cepdnaclk/e17-3yp-remote-keyboard-tutoring-system/Research/Backend Technologies/Nginx/README.md

# Why Choose NGINX?
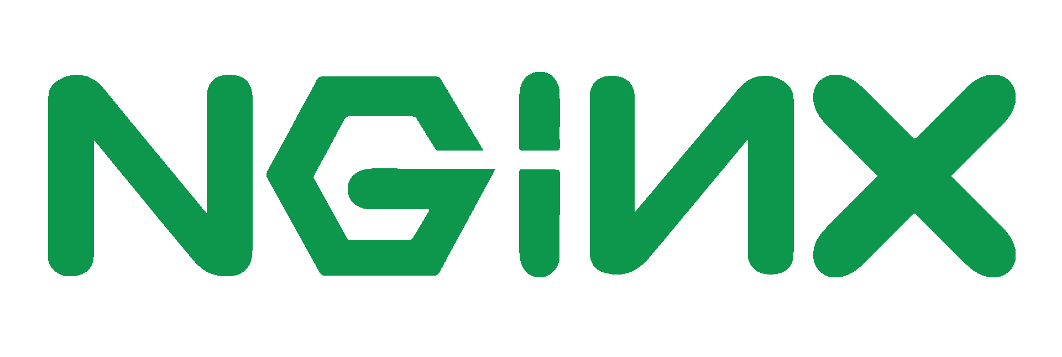
[picture p58: Research/Backend Technologies/Nginx/images/nginx_logo.png]


## What is NGINX ?
NGINX is open source software for web serving, reverse proxying, caching, load balancing, media streaming, and more. It started out as a web server designed for maximum performance and stability. In addition to its HTTP server capabilities, NGINX can also function as a proxy server for email (IMAP, POP3, and SMTP) and a reverse proxy and load balancer for HTTP, TCP, and UDP servers.

## Features of NGINX

- As a software‑only all-in-one load balancer, web server, API gateway, and reverse proxy that is designed for cloud‑native architectures, NGINX helps you accelerate your IT infrastructure and application modernization efforts. NGINX Plus delivers enterprise‑grade capabilities that provide robust reliability and security.
- NGINX is a multifunction tool. With NGINX, you can use the same tool as your load balancer, reverse proxy, content cache, and web server, minimizing the amount of tooling and configuration your organization needs to maintain. NGINX offers documentation and a wide array of eBooks, webinars, and videos to get you on your feet. NGINX Plus includes rapid‑response customer support, so you can easily get help diagnosing any part of your stack that uses NGINX or NGINX Plus.
- NGINX keeps evolving. For the past decade NGINX has been at the forefront of development of the modern Web, and has helped lead the way on everything from HTTP/2 to microservices support. As development and delivery of web applications continue to evolve, NGINX Plus keeps adding features to enable flawless application delivery, from support for configuration using an implementation of JavaScript customized for NGINX, to support for dynamic modules. Using NGINX Plus ensures you’ll stay at the cutting edge of web performance.

## How NGINX benefit Us ?
We will be using NGINX as a reverse proxy so that we can access it through http, https along with Let’s Encrypt to create and manage free validated SSL/TLS certificates. 

It’s well known that SSL/TLS encryption of your website leads to higher search rankings and better security for your users. However, there are a number of barriers that have prevented website owners from adopting SSL.Two of the biggest barriers have been the cost and the manual processes involved in getting a certificate. But now, with Let’s Encrypt, they are no longer a concern. Let’s Encrypt makes SSL/TLS encryption freely available to everyone.

### Let's Encrypt -
is a free, automated, and open certificate authority (CA). Certificates issued by Let’s Encrypt are trusted by most browsers today, including older browsers such as Internet Explorer on Windows XP SP3. In addition, Let’s Encrypt fully automates both issuing and renewing of certificates.

**[click here](#) to see how we deply our apps, APIs with NGINX and Let's Encrypt**
