cepdnaclk/e17-3yp-remote-keyboard-tutoring-system/docs/images/about02.gif

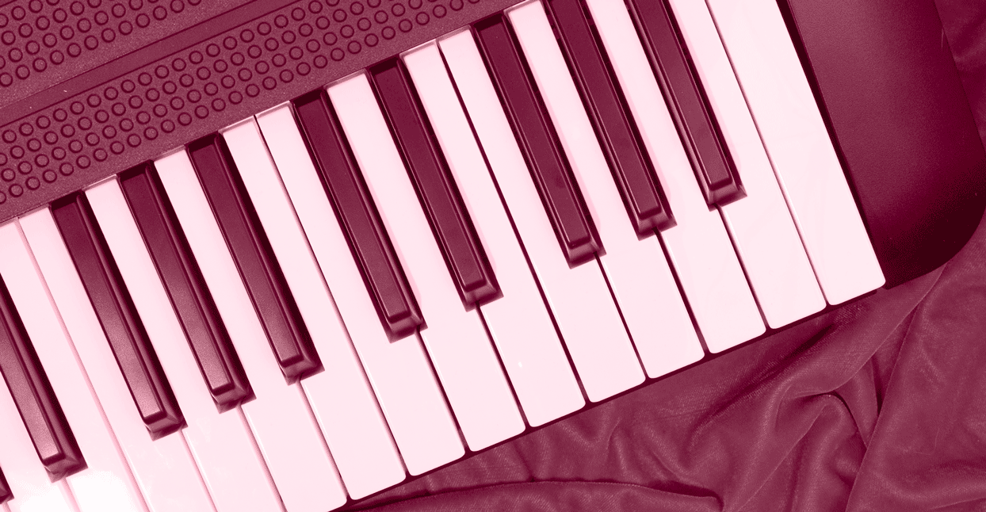
docs/images/about02.gif
