cepdnaclk/e17-3yp-remote-keyboard-tutoring-system/docs/images/about-2.jpg

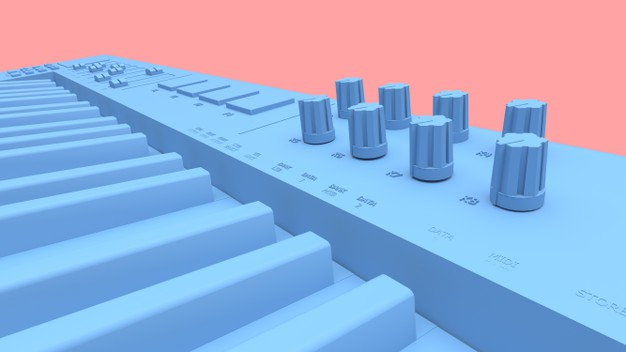
docs/images/about-2.jpg
