cepdnaclk/e17-3yp-remote-keyboard-tutoring-system/docs/images/FlowOfData1.png

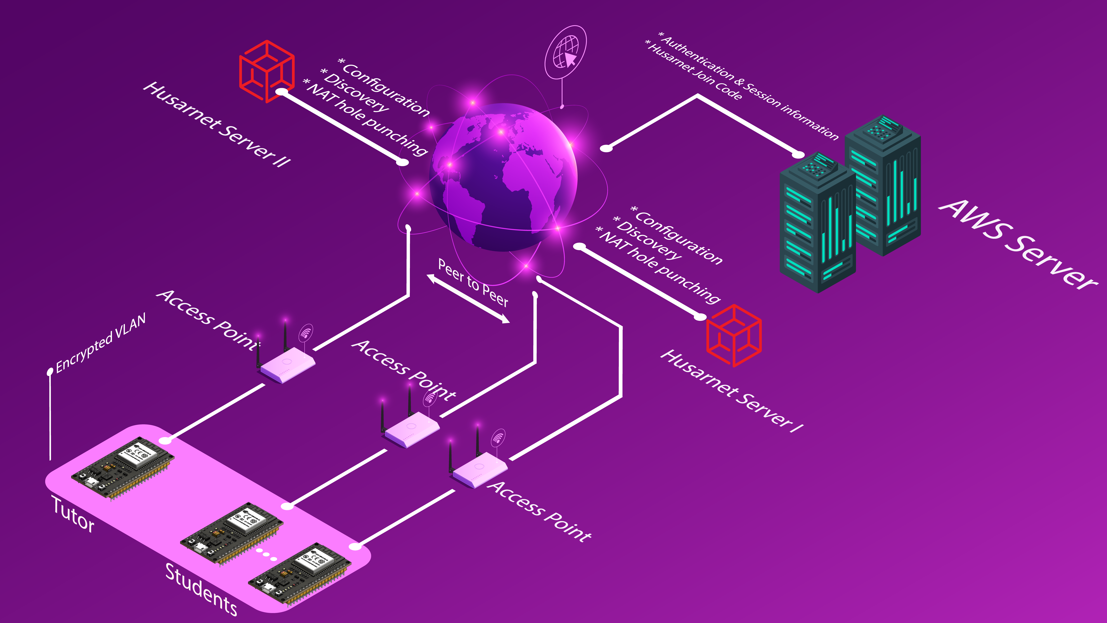
docs/images/FlowOfData1.png
