cepdnaclk/e17-3yp-remote-keyboard-tutoring-system/docs/images/MobileUIgif.gif

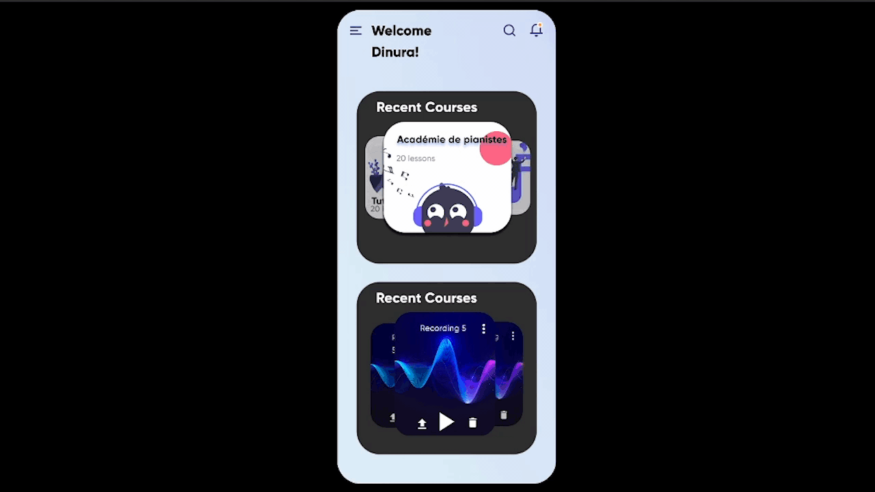
docs/images/MobileUIgif.gif
