cepdnaclk/e17-3yp-remote-keyboard-tutoring-system/docs/images/placeholder-mobile.png

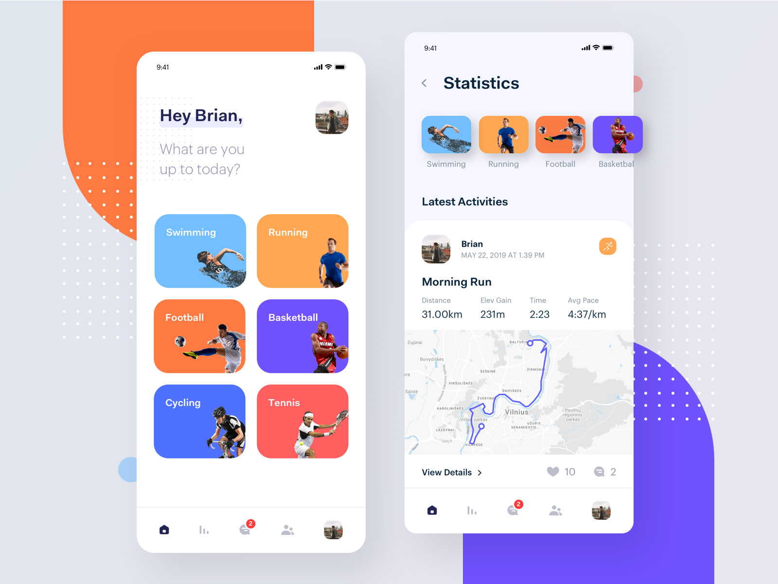
docs/images/placeholder-mobile.png
