cepdnaclk/e17-3yp-remote-keyboard-tutoring-system/docs/images/placeholder-web.png

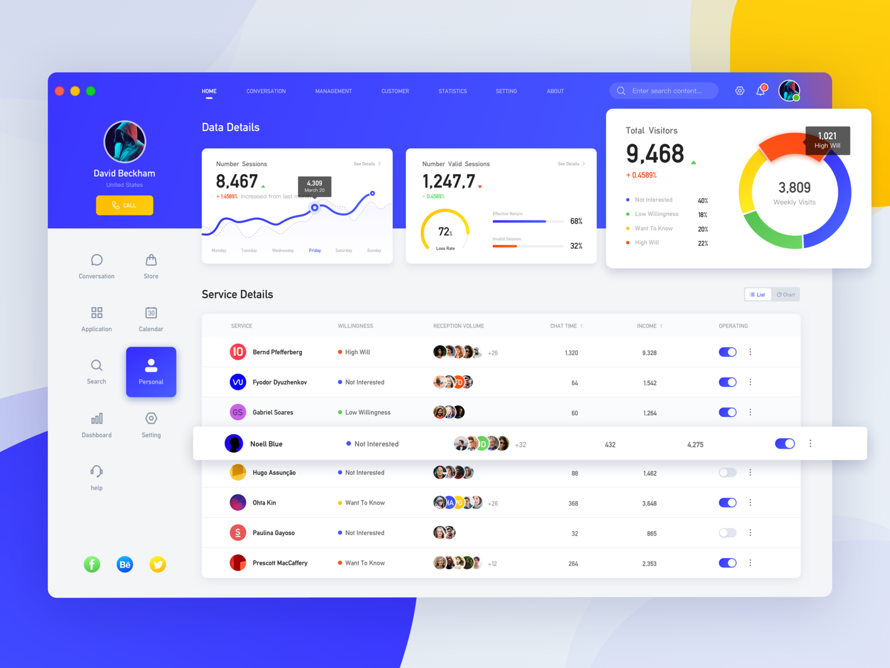
docs/images/placeholder-web.png
