cepdnaclk/e17-3yp-remote-keyboard-tutoring-system/docs/images/Processing Unit 2.jpg

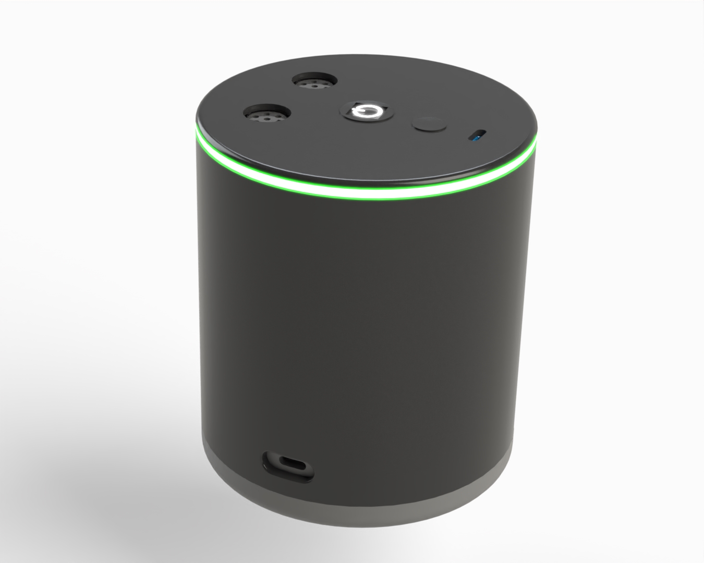
docs/images/Processing Unit 2.jpg
