cepdnaclk/e17-3yp-remote-keyboard-tutoring-system/docs/images/pu.png

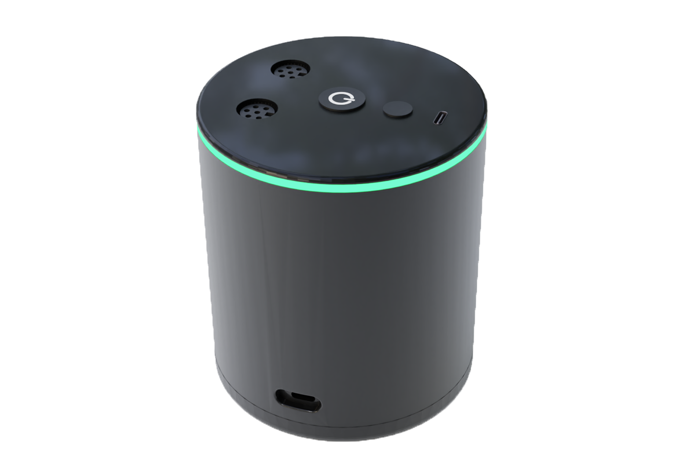
docs/images/pu.png
