cepdnaclk/e17-3yp-remote-keyboard-tutoring-system/docs/images/Remote-Keyboard-Tutor.gif

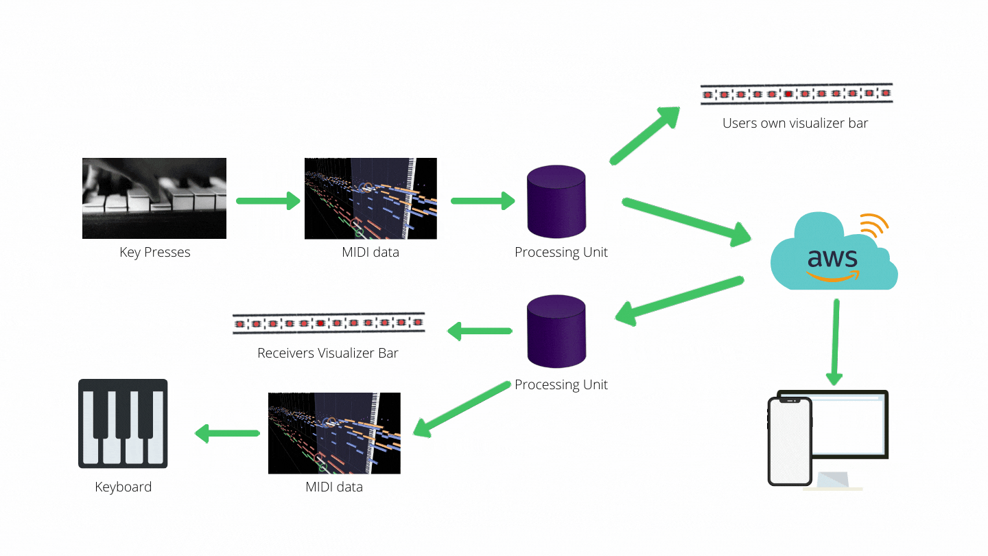
docs/images/Remote-Keyboard-Tutor.gif
