cepdnaclk/e17-3yp-remote-keyboard-tutoring-system/docs/images/Remote-Keyboard-Tutor.png

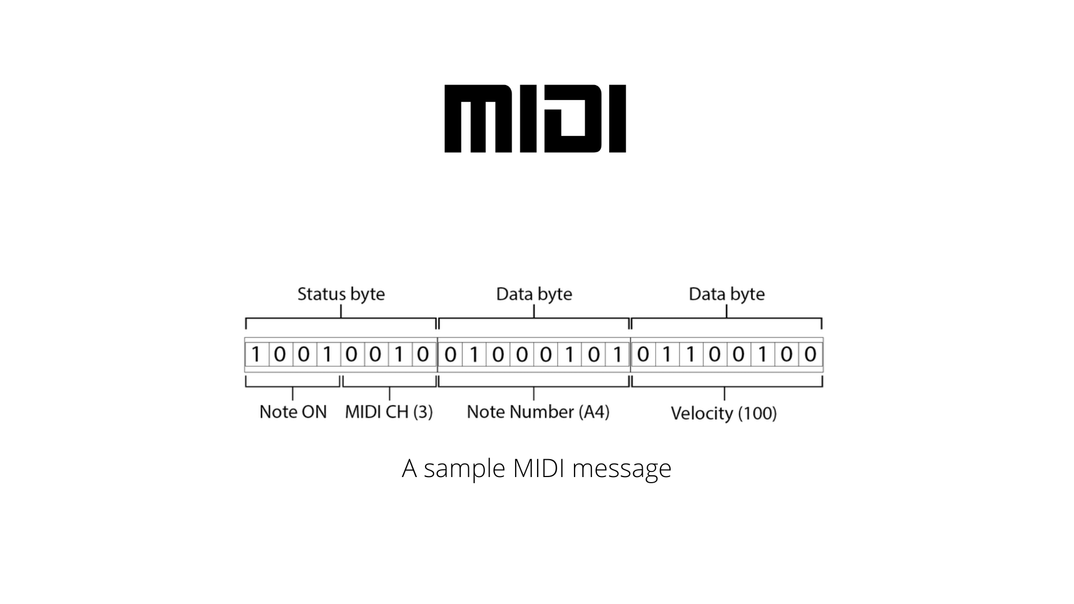
docs/images/Remote-Keyboard-Tutor.png
