cepdnaclk/e17-3yp-remote-keyboard-tutoring-system/docs/images/view1.png

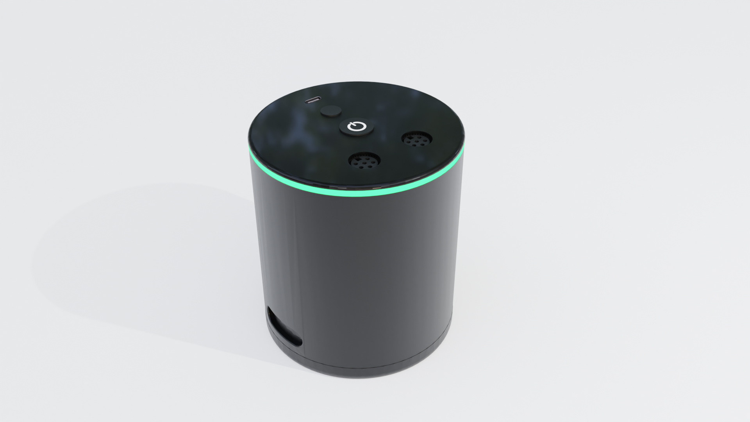
docs/images/view1.png
