cepdnaclk/e17-3yp-remote-keyboard-tutoring-system/docs/images/view3.png

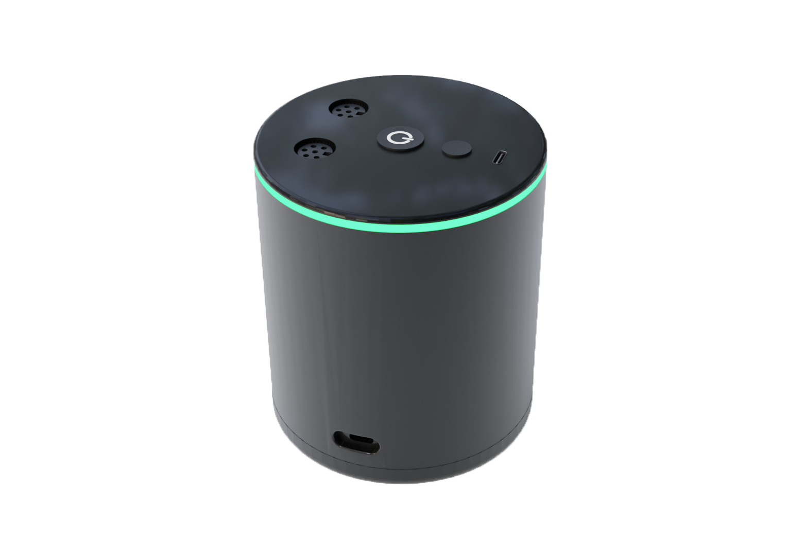
docs/images/view3.png
