cepdnaclk/e17-3yp-remote-keyboard-tutoring-system/docs/images/Visualizer Block.jpg

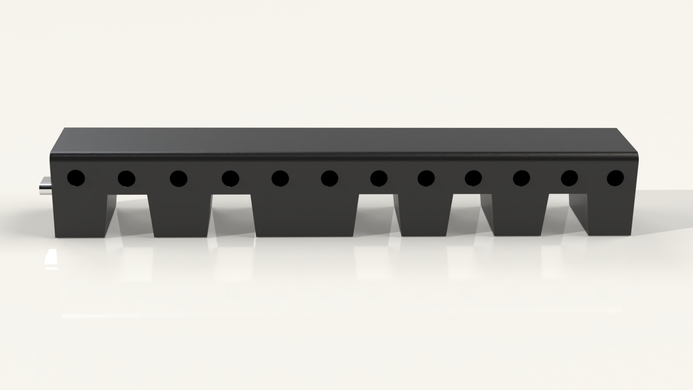
docs/images/Visualizer Block.jpg
