cepdnaclk/e17-3yp-remote-keyboard-tutoring-system/docs/images/visualizerBaeW.png

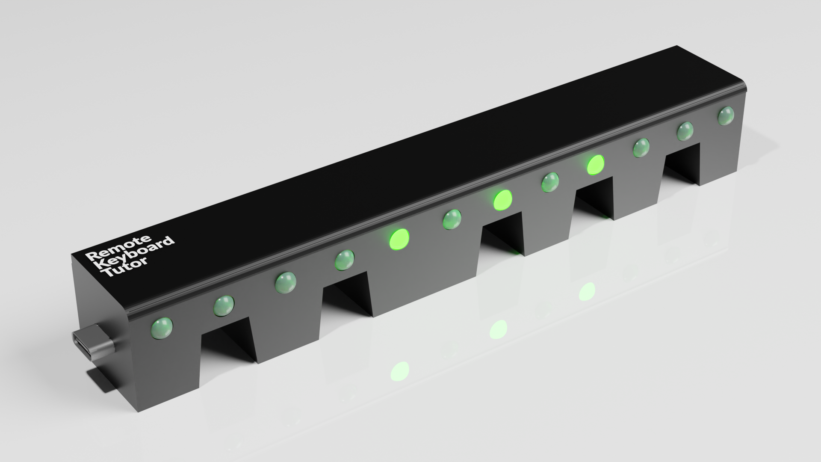
docs/images/visualizerBaeW.png
