cepdnaclk/e17-3yp-remote-keyboard-tutoring-system/docs/images/visualizerBar.png

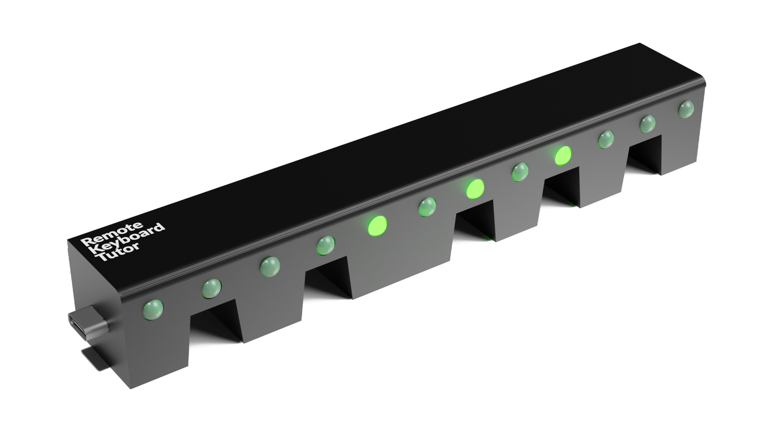
docs/images/visualizerBar.png
