cepdnaclk/e17-3yp-remote-keyboard-tutoring-system/docs/images/visualizerBarB.png

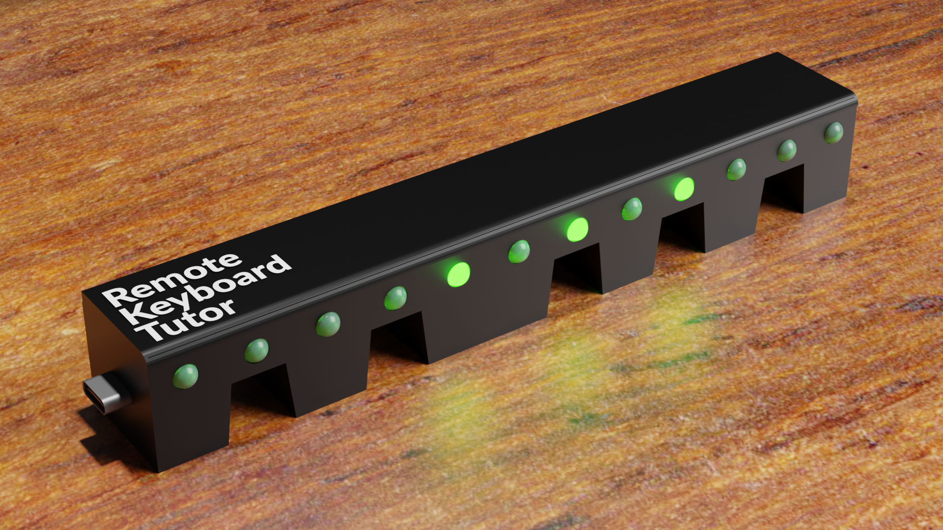
docs/images/visualizerBarB.png
