cepdnaclk/e17-3yp-remote-keyboard-tutoring-system/docs/midi-message-taxonomy.png

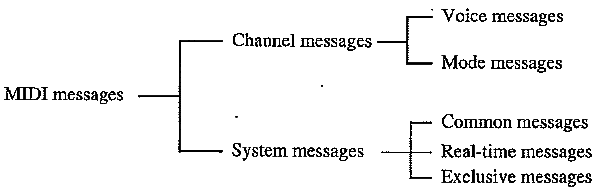
docs/midi-message-taxonomy.png
