cepdnaclk/e17-3yp-remote-keyboard-tutoring-system/docs/protocol.png

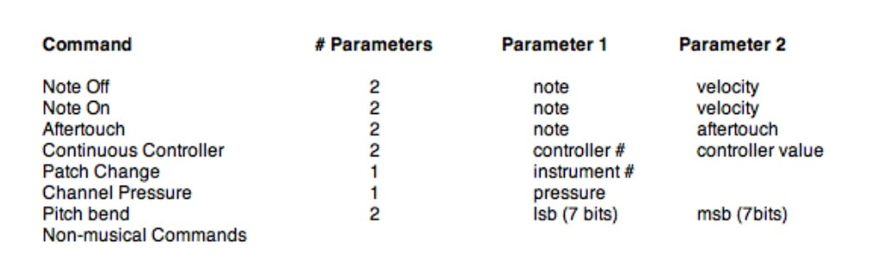
docs/protocol.png
