cepdnaclk/e17-3yp-remote-keyboard-tutoring-system/Hardware/Schematics/Arduino-Pro-Micro-Pinout.jpg

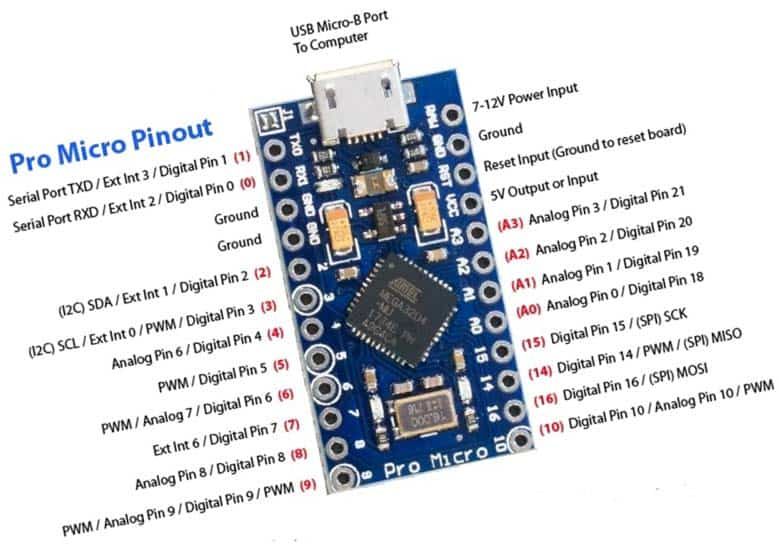
Hardware/Schematics/Arduino-Pro-Micro-Pinout.jpg
