cepdnaclk/e17-3yp-remote-keyboard-tutoring-system/Hardware/Schematics/DIN 5 pin connector pinout.jpg

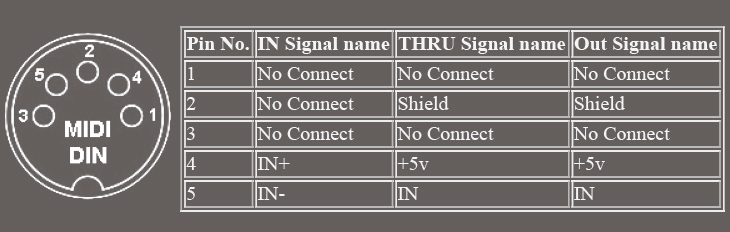
Hardware/Schematics/DIN 5 pin connector pinout.jpg
