cepdnaclk/e17-3yp-remote-keyboard-tutoring-system/Hardware/Schematics/pro-mini-pinout.jpeg

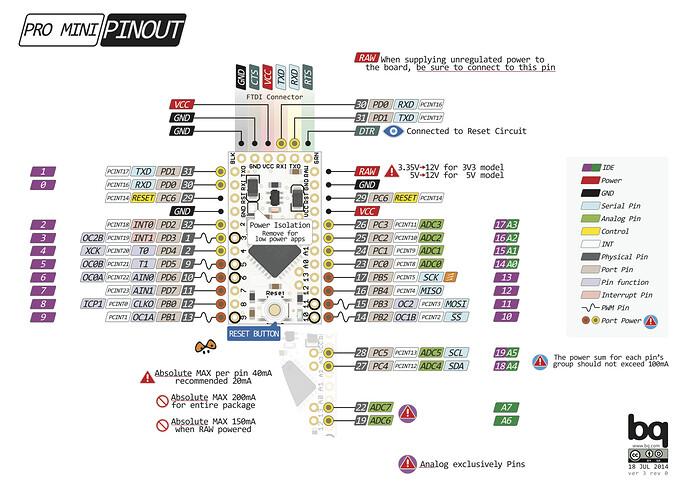
Hardware/Schematics/pro-mini-pinout.jpeg
