cepdnaclk/e17-3yp-remote-keyboard-tutoring-system/Hardware/Schematics/Processing Unit.png

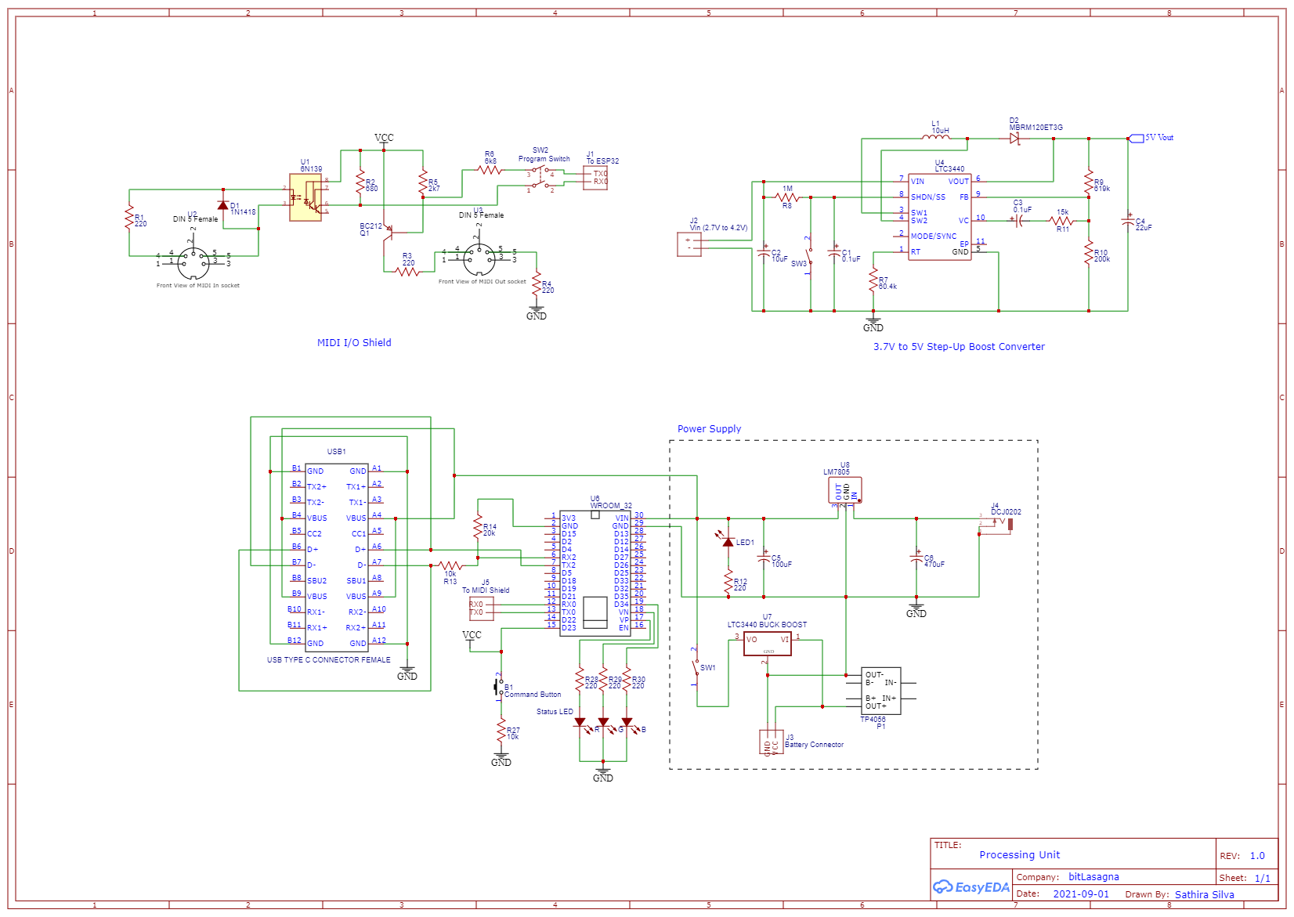
Hardware/Schematics/Processing Unit.png
