cepdnaclk/e17-3yp-remote-keyboard-tutoring-system/Mobile App/ForteApp/MobileApp/assets/3e8c7e1767d023deecac1b5b417257c0.jpg

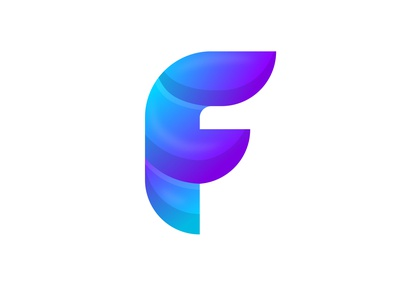
Mobile App/ForteApp/MobileApp/assets/3e8c7e1767d023deecac1b5b417257c0.jpg
