cepdnaclk/e17-3yp-remote-keyboard-tutoring-system/Mobile App/ForteApp/MobileApp/assets/home.png

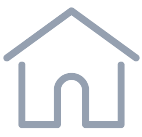
Mobile App/ForteApp/MobileApp/assets/home.png
