cepdnaclk/e17-3yp-remote-keyboard-tutoring-system/Mobile App/ForteApp/MobileApp/assets/M2.jpg

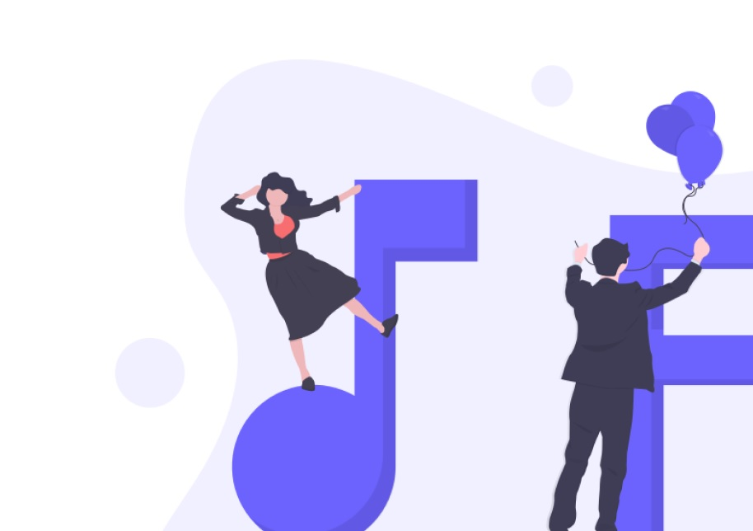
Mobile App/ForteApp/MobileApp/assets/M2.jpg
