cepdnaclk/e17-3yp-remote-keyboard-tutoring-system/Mobile App/ForteApp/MobileApp/assets/M3.jpg

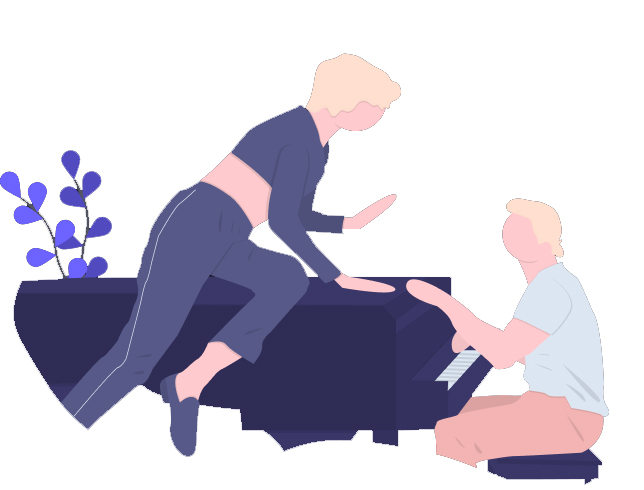
Mobile App/ForteApp/MobileApp/assets/M3.jpg
