cepdnaclk/e17-3yp-remote-keyboard-tutoring-system/Mobile App/ForteApp/MobileApp/assets/settings.png

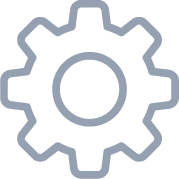
Mobile App/ForteApp/MobileApp/assets/settings.png
