cepdnaclk/e17-3yp-remote-keyboard-tutoring-system/server/src/database_schema/forte-er.jpeg

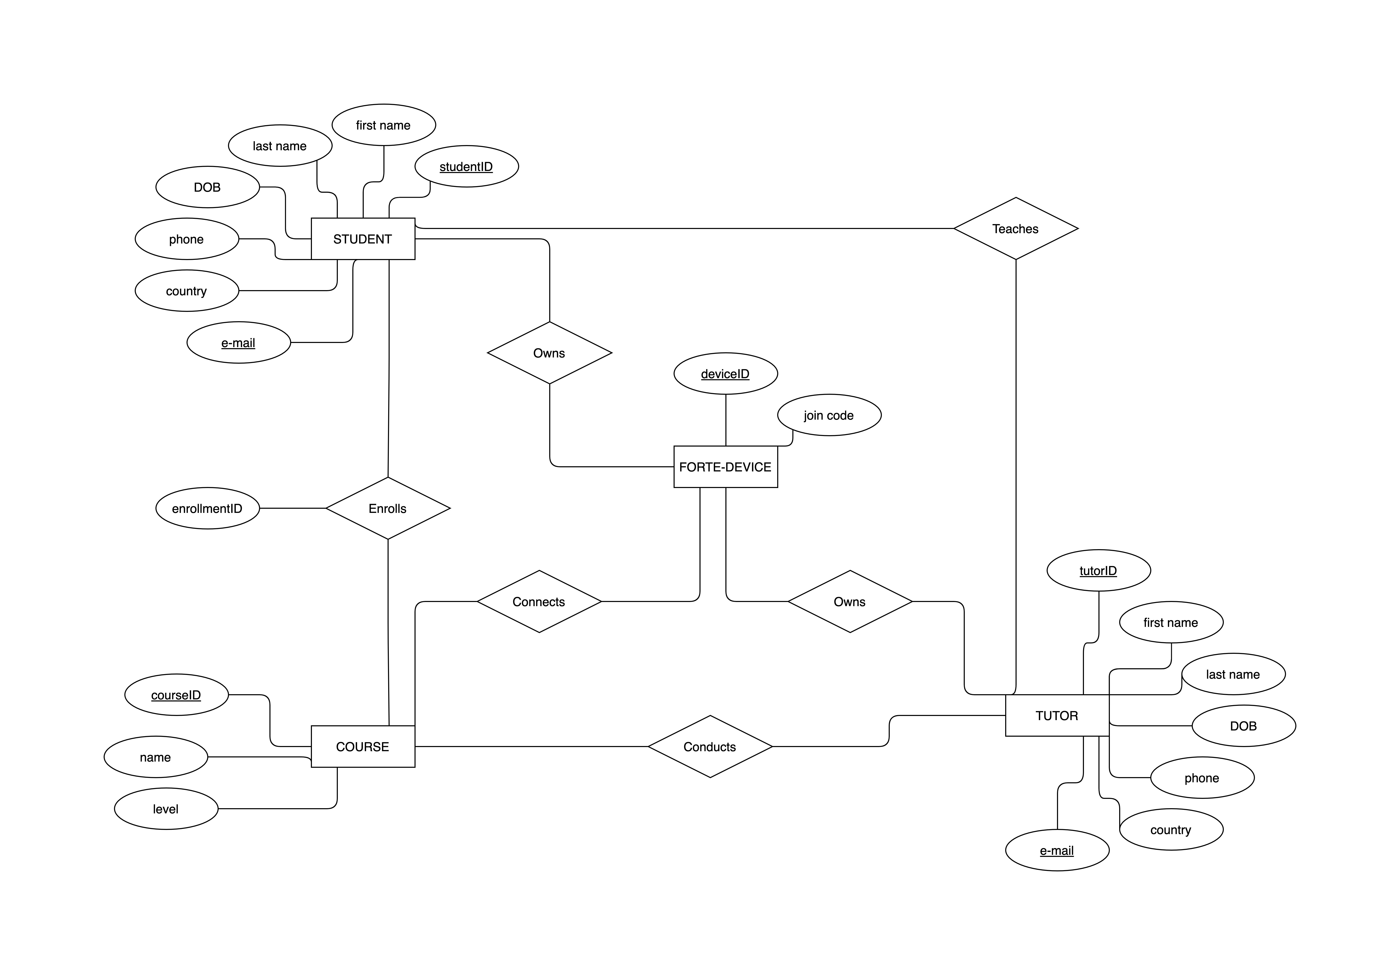
server/src/database_schema/forte-er.jpeg
