cepdnaclk/e17-3yp-remote-keyboard-tutoring-system/server/src/uploads/courses/cover-upload_dateVal_1634644308922_photo-1552422535-c45813c61732.jpg

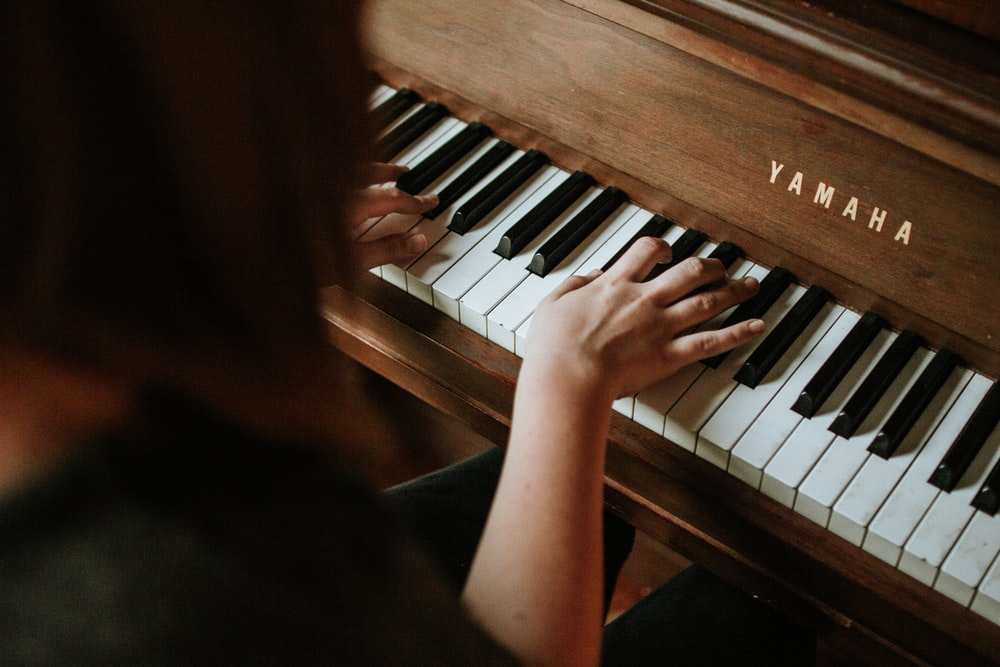
server/src/uploads/courses/cover-upload_dateVal_1634644308922_photo-1552422535-c45813c61732.jpg
