cepdnaclk/e17-3yp-remote-keyboard-tutoring-system/server/src/uploads/courses/cover-upload_dateVal_1634646680036_Piano-Hands-Play-HD-Wallpapers-Free-Download.jpg

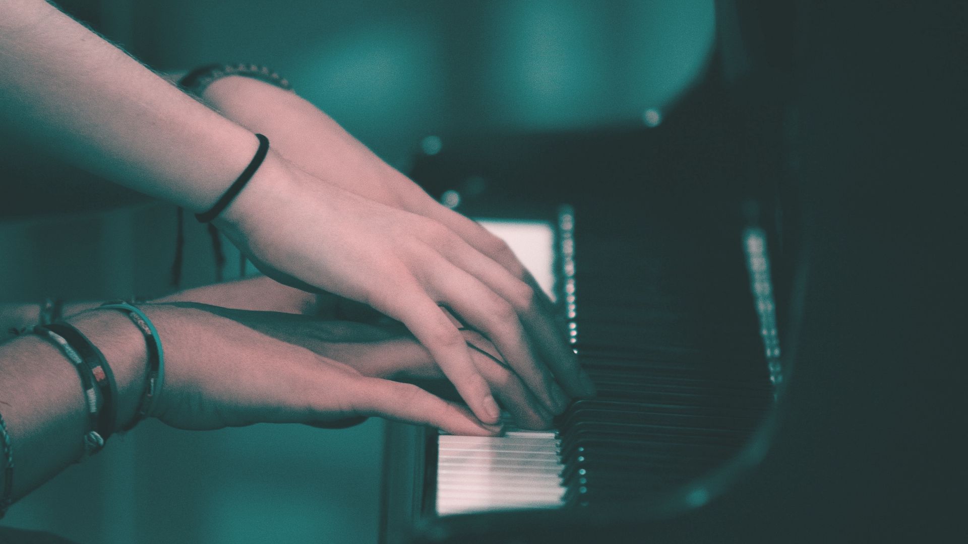
server/src/uploads/courses/cover-upload_dateVal_1634646680036_Piano-Hands-Play-HD-Wallpapers-Free-Download.jpg
