cepdnaclk/e17-3yp-remote-keyboard-tutoring-system/server/src/uploads/courses/cover-upload_dateVal_1634693529020_cd62944dfa67ef2cf75b0063e259fd68.jpg

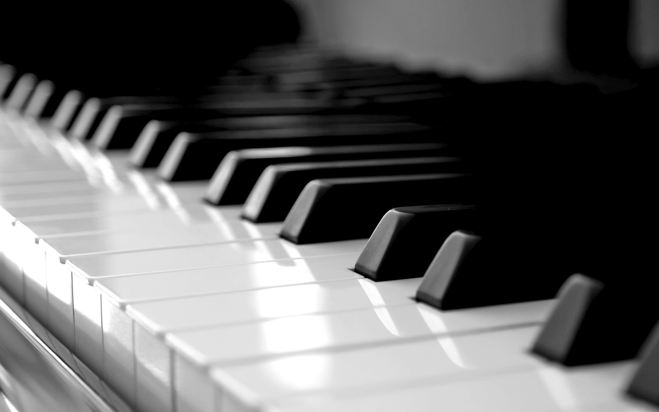
server/src/uploads/courses/cover-upload_dateVal_1634693529020_cd62944dfa67ef2cf75b0063e259fd68.jpg
