cepdnaclk/e17-3yp-remote-keyboard-tutoring-system/server/src/uploads/courses/cover-upload_dateVal_1634815107962_piano-anime.gif

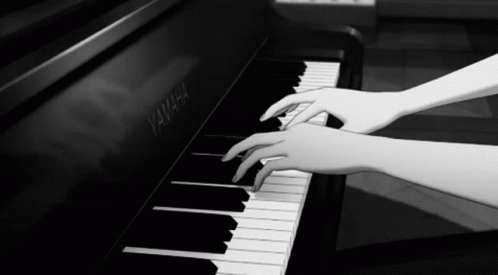
server/src/uploads/courses/cover-upload_dateVal_1634815107962_piano-anime.gif
