cepdnaclk/e17-3yp-remote-keyboard-tutoring-system/server/src/uploads/courses/cover-upload_dateVal_1634815645119_piano-white-classical-lacquer.jpg

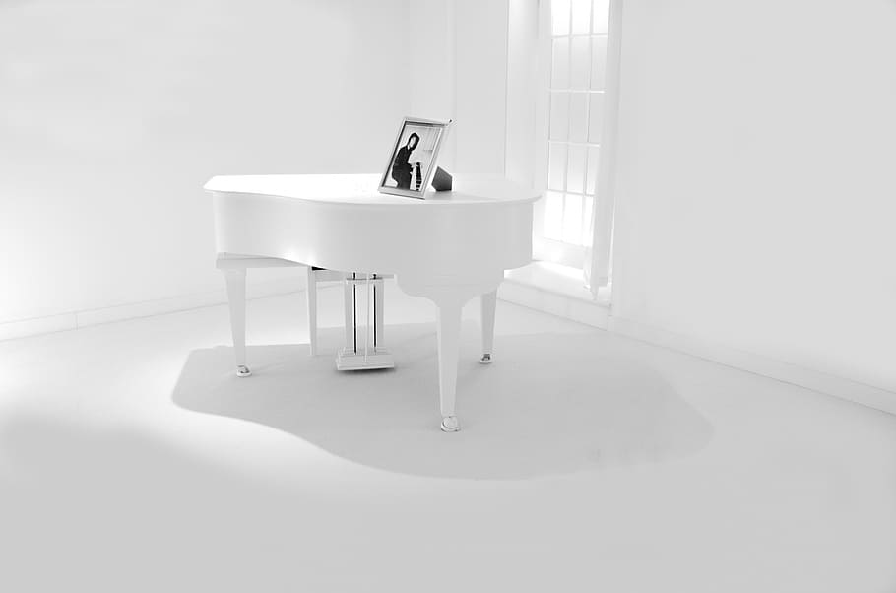
server/src/uploads/courses/cover-upload_dateVal_1634815645119_piano-white-classical-lacquer.jpg
