cepdnaclk/e17-3yp-remote-keyboard-tutoring-system/server/src/uploads/courses/cover-upload_dateVal_1634832013604_Blue-hair-anime-girl-play-piano_2560x1440.jpg

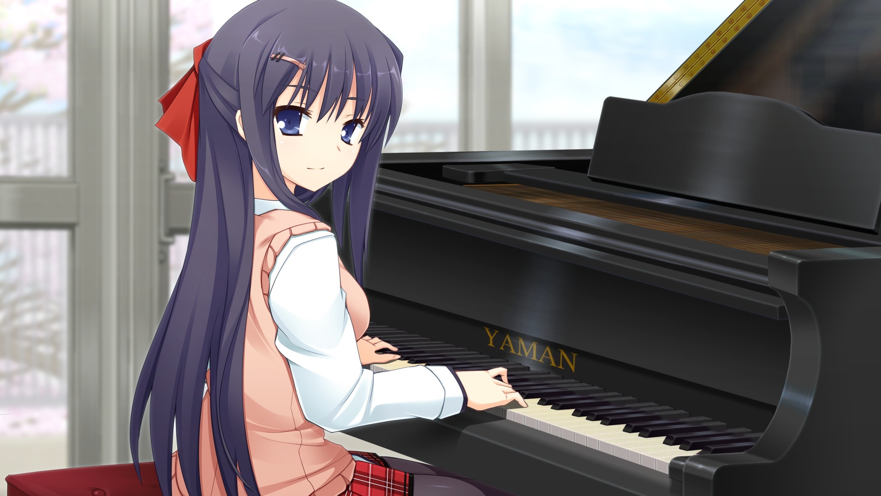
server/src/uploads/courses/cover-upload_dateVal_1634832013604_Blue-hair-anime-girl-play-piano_2560x1440.jpg
