cepdnaclk/e17-3yp-remote-keyboard-tutoring-system/UI-UX/Web/images/First.jpg

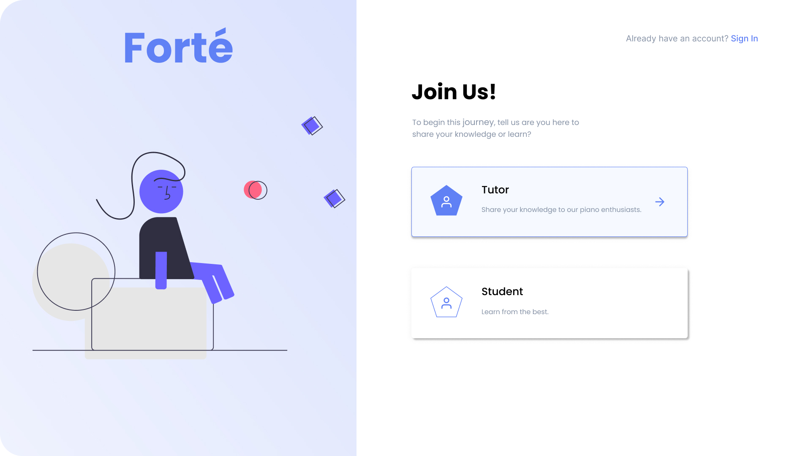
UI-UX/Web/images/First.jpg
