cepdnaclk/e17-3yp-remote-keyboard-tutoring-system/web-app/src/assets/images/Cover 1.jpg

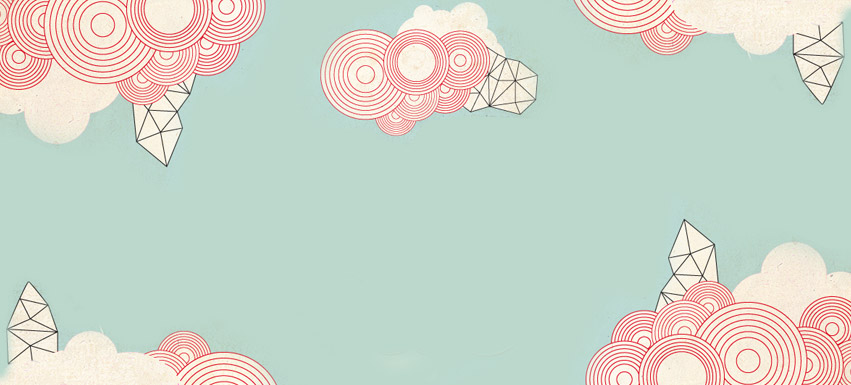
web-app/src/assets/images/Cover 1.jpg
