cepdnaclk/e17-3yp-remote-keyboard-tutoring-system/web-app/src/components/TileList/Default Backgrounds/bg1.jpg

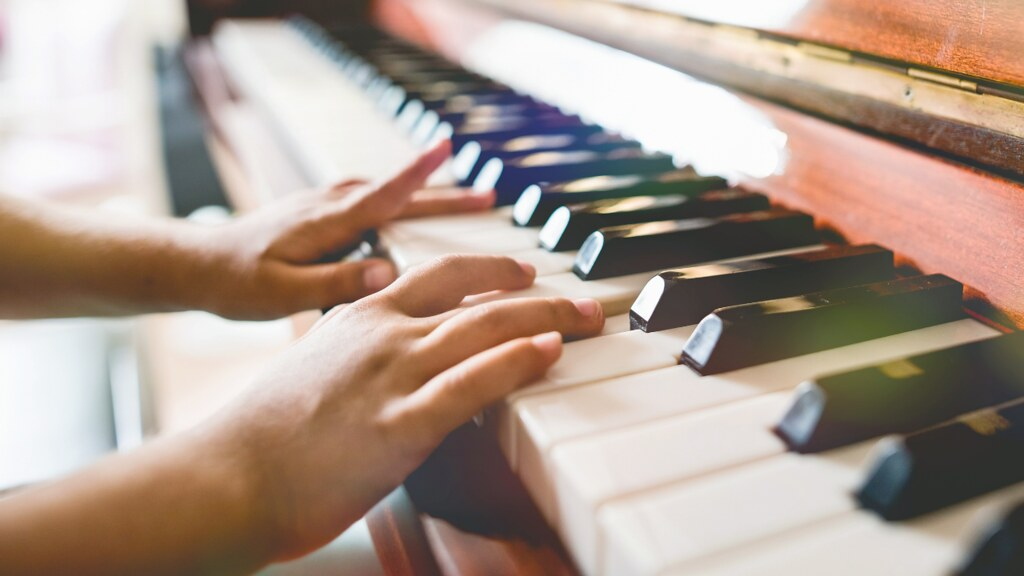
web-app/src/components/TileList/Default Backgrounds/bg1.jpg
