cepdnaclk/e17-3yp-remote-keyboard-tutoring-system/web-app/src/assets/images/email-id-verification.png

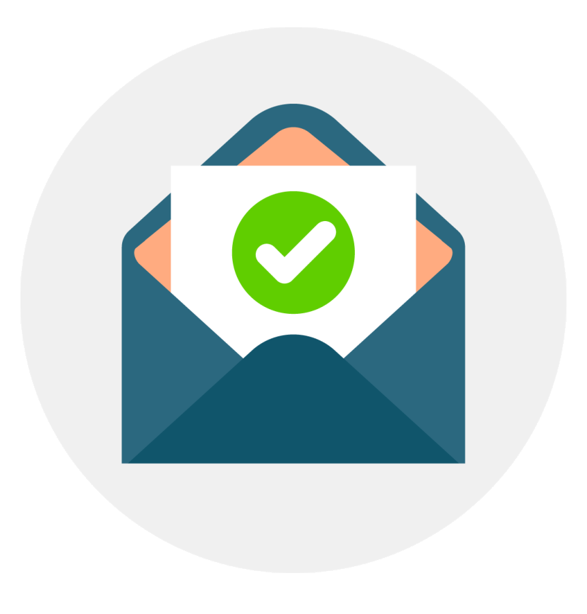
web-app/src/assets/images/email-id-verification.png
