cepdnaclk/e17-3yp-remote-keyboard-tutoring-system/Research/ESP32/ESP-IDF-Tests/wifiConnect/main/main.c

#include <stdio.h>
#include "freertos/FreeRTOS.h"
#include "freertos/task.h"
#include "freertos/event_groups.h"
#include "esp_system.h"
#include "esp_wifi.h"
#include "esp_spi_flash.h"
#include "esp_log.h"
#include "nvs_flash.h"

#define WIFI_SSID "SSID"
#define WIFI_PASS "PASSWORD"
#define MAXIMUM_RETRY  10

/* FreeRTOS event group to signal when we are connected*/
static EventGroupHandle_t s_wifi_event_group;

/* The event group allows multiple bits for each event, but we only care about two events:
 * - we are connected to the AP with an IP
 * - we failed to connect after the maximum amount of retries
 */
#define WIFI_CONNECTED_BIT BIT0
#define WIFI_FAIL_BIT      BIT1

static const char *TAG = "Wifi Station";

static int s_retry_num = 0;

static void event_handler(void* arg, esp_event_base_t event_base, int32_t event_id, void* event_data) {
    if (event_base == WIFI_EVENT && event_id == WIFI_EVENT_STA_START)
        esp_wifi_connect();                                 // Connect the ESP32 WiFi station to the AP.
    else if (event_base == WIFI_EVENT && event_id == WIFI_EVENT_STA_DISCONNECTED) {
        if (s_retry_num < MAXIMUM_RETRY) {
            esp_wifi_connect();
            s_retry_num++;
            ESP_LOGI(TAG, "retry to connect to the AP");
        } 
        else
            xEventGroupSetBits(s_wifi_event_group, WIFI_FAIL_BIT);
        ESP_LOGI(TAG, "connect to the AP fail");
    }
    else if (event_base == IP_EVENT && event_id == IP_EVENT_STA_GOT_IP) {
        ip_event_got_ip_t* event = (ip_event_got_ip_t*) event_data;
        ESP_LOGI(TAG, "got ip:" IPSTR, IP2STR(&event->ip_info.ip));
        s_retry_num = 0;
        xEventGroupSetBits(s_wifi_event_group, WIFI_CONNECTED_BIT);
    }
}

void wifi_init_sta(void) {
    s_wifi_event_group = xEventGroupCreate();               // Allocate the event group.
    ESP_ERROR_CHECK(esp_netif_init());                      // Initialize the underlying TCP/IP stack.
    ESP_ERROR_CHECK(esp_event_loop_create_default());       // Start the default event loop.
    esp_netif_create_default_wifi_sta();                    // Creates default WIFI STA. In case of any init error this API aborts.

    wifi_init_config_t conf = WIFI_INIT_CONFIG_DEFAULT();   // Macro for the default configuration.
    ESP_ERROR_CHECK(esp_wifi_init(&conf));                  // Initialize the WiFi driver.

    esp_event_handler_instance_t instance_any_id;
    esp_event_handler_instance_t instance_got_ip;

    // Register an instance of event handler to the default loop.
    ESP_ERROR_CHECK(esp_event_handler_instance_register(WIFI_EVENT,         // The base id of the event to register the handler for.
                                                        ESP_EVENT_ANY_ID,   // The id of the event to register the handler for.
                                                        &event_handler,     // The handler function which gets called when the event is dispatched.
                                                        NULL,               // Data, aside from event data, that is passed to the handler when it is called
                                                        &instance_any_id)); // An event handler instance object related to the registered event handler and data, can be NULL.
    ESP_ERROR_CHECK(esp_event_handler_instance_register(IP_EVENT,
                                                        IP_EVENT_STA_GOT_IP,
                                                        &event_handler,
                                                        NULL,
                                                        &instance_got_ip));

    // Configuration data for ESP32 AP or STA.
    wifi_config_t wifi_config = {
        .sta = {
            .ssid = WIFI_SSID,
            .password = WIFI_PASS,
            /* Setting a password implies station will connect to all security modes including WEP/WPA.
             * However these modes are deprecated and not advisable to be used. Incase your Access point
             * doesn't support WPA2, these mode can be enabled by commenting below line */
	        .threshold.authmode = WIFI_AUTH_WPA2_PSK,

            .pmf_cfg = {
                .capable = true,
                .required = false
            },
        },
    };

    ESP_ERROR_CHECK(esp_wifi_set_mode(WIFI_MODE_STA));                      // Set the WiFi mode to station.
    ESP_ERROR_CHECK(esp_wifi_set_config(WIFI_IF_STA, &wifi_config));        // Set the configuration of the ESP32 STA or AP.
    ESP_ERROR_CHECK(esp_wifi_start());                                      // Start the WiFi driver.

    ESP_LOGI(TAG, "wifi_init_sta finished.");

    /* Waiting until either the connection is established (WIFI_CONNECTED_BIT) or connection failed for the maximum
     * number of re-tries (WIFI_FAIL_BIT). The bits are set by event_handler() (see above) 
     */
    EventBits_t bits = xEventGroupWaitBits(s_wifi_event_group,
            WIFI_CONNECTED_BIT | WIFI_FAIL_BIT,
            pdFALSE,
            pdFALSE,
            portMAX_DELAY);

    /* xEventGroupWaitBits() returns the bits before the call returned, hence we can test which event actually
     * happened. */
    if (bits & WIFI_CONNECTED_BIT)
        ESP_LOGI(TAG, "connected to ap SSID:%s password:%s", WIFI_SSID, WIFI_PASS);
    else if (bits & WIFI_FAIL_BIT)
        ESP_LOGI(TAG, "Failed to connect to SSID:%s, password:%s", WIFI_SSID, WIFI_PASS);
    else
        ESP_LOGE(TAG, "UNEXPECTED EVENT");

    /* The event will not be processed after unregister */
    ESP_ERROR_CHECK(esp_event_handler_instance_unregister(IP_EVENT, IP_EVENT_STA_GOT_IP, instance_got_ip));
    ESP_ERROR_CHECK(esp_event_handler_instance_unregister(WIFI_EVENT, ESP_EVENT_ANY_ID, instance_any_id));
    vEventGroupDelete(s_wifi_event_group);
}

void app_main(void) {
    //Initialize NVS
    esp_err_t ret = nvs_flash_init();
    if (ret == ESP_ERR_NVS_NO_FREE_PAGES || ret == ESP_ERR_NVS_NEW_VERSION_FOUND) {
      ESP_ERROR_CHECK(nvs_flash_erase());
      ret = nvs_flash_init();
    }
    ESP_ERROR_CHECK(ret);

    ESP_LOGI(TAG, "ESP_WIFI_MODE_STA");

    wifi_init_sta();
}
