cepdnaclk/e17-3yp-remote-keyboard-tutoring-system/Hardware/Visualizer Block Communication/SoftwareSerial/SoftwareSerial Communication Test/slave/slave.ino

#include <SoftwareSerial.h>

SoftwareSerial ArduinoMaster(2, 3);

char cmd = "";
char old_cmd;

void setup() {
  ArduinoMaster.begin(9600);
}

void loop() {
  old_cmd = cmd;
  // Read data from master
  if (ArduinoMaster.available()) {
    cmd = ArduinoMaster.read();
  }
  // Send answer to master
  if (cmd != old_cmd) {
    ArduinoMaster.write(cmd);
  }
}
